ThomasStolt/Stair-Light-Project/images/IMG_1906.jpg

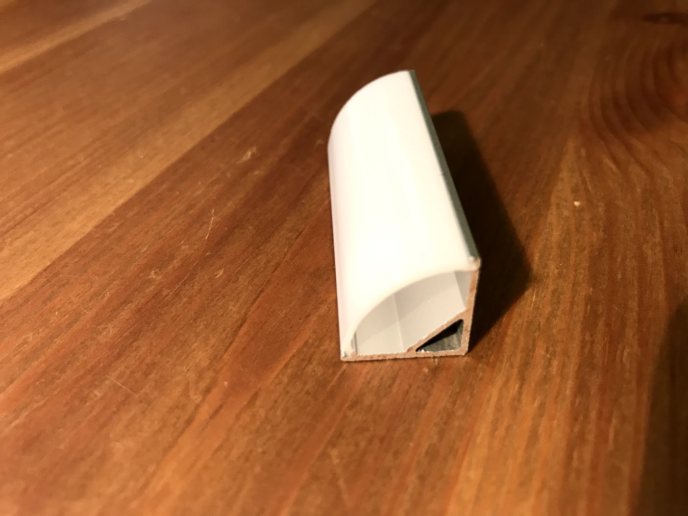
images/IMG_1906.jpg
