ThomasStolt/Stair-Light-Project/images/IMG_1907.jpg

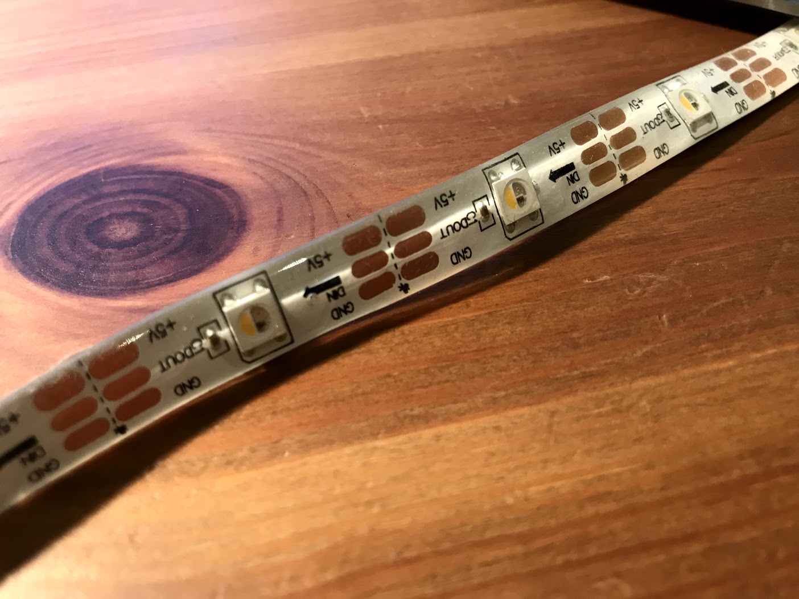
images/IMG_1907.jpg
