ThomasStolt/Stair-Light-Project/images/IMG_1908.jpg

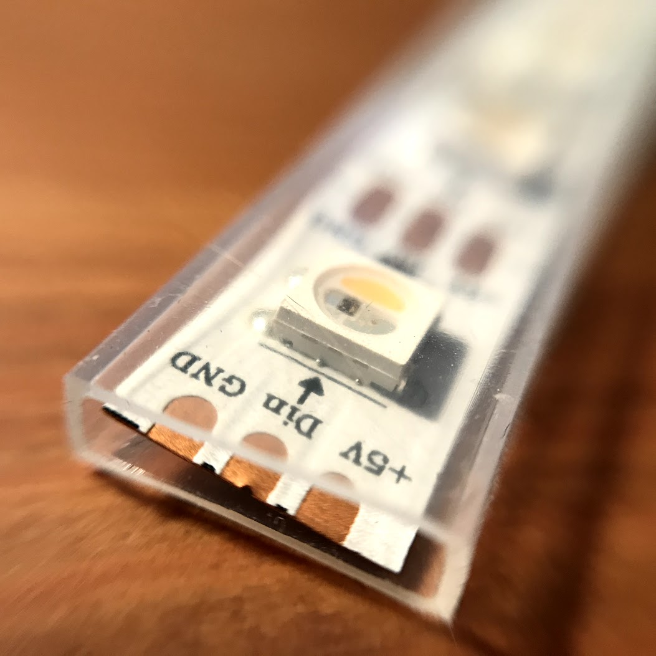
images/IMG_1908.jpg
