ThomasStolt/Stair-Light-Project/images/IMG_1909.jpg

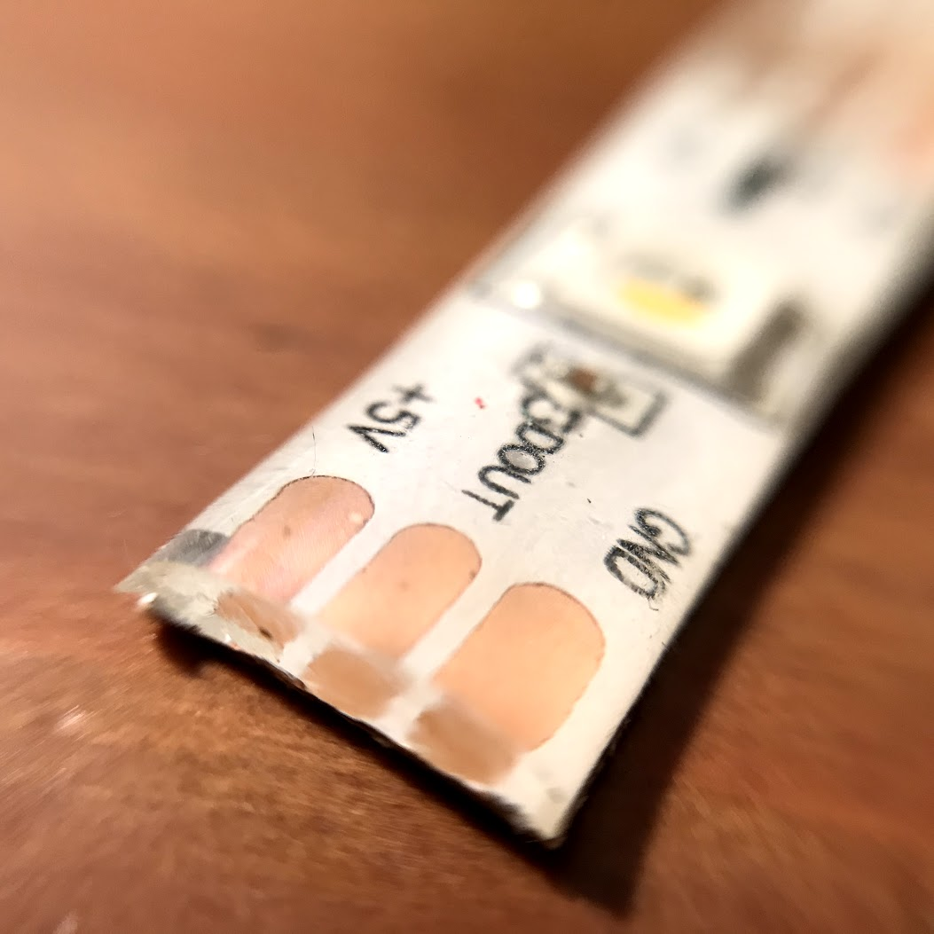
images/IMG_1909.jpg
