ThomasStolt/Stair-Light-Project/images/IMG_1958.jpg

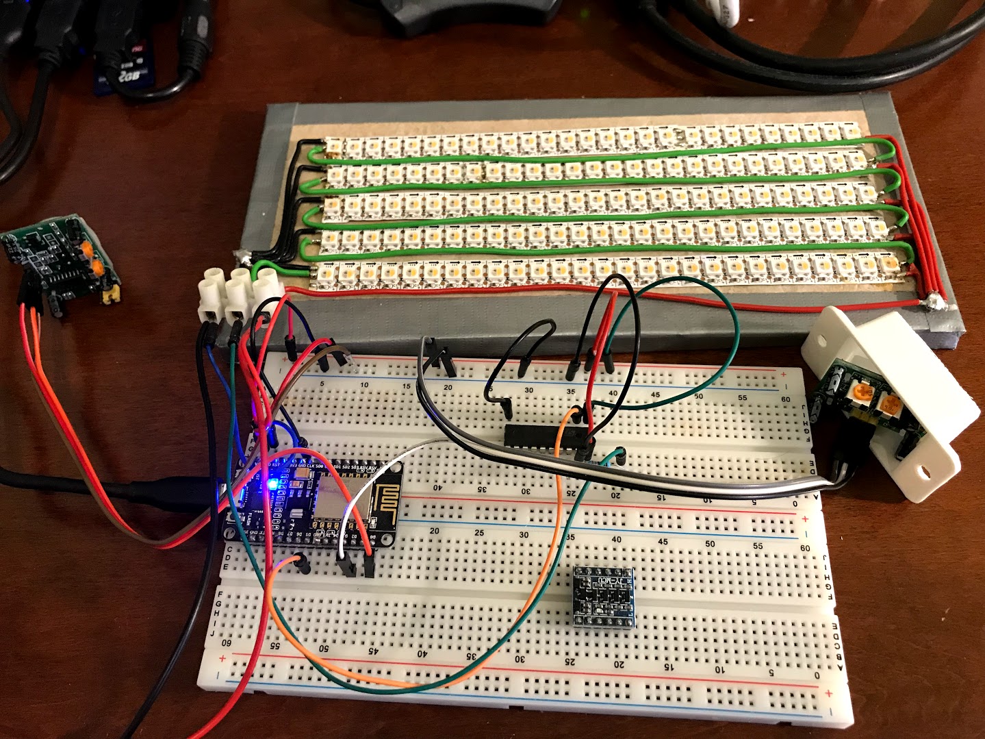
images/IMG_1958.jpg
